JoaoVCMiranda/PSI3422/experiências/Exp3_PSI3422/modelo_1/print/hw201_bracket.scad

include <../parts/params.scad>
use <../parts/hw201_mount.scad>

hw201_bracket_3d(0, 0);
