JoaoVCMiranda/PSI3422/experiências/Exp3_PSI3422/modelo_3/print/hw201_bracket.scad

// Suporte do sensor HW-201 — imprimir 2x (um por roda, são idênticos,
// só a posição de montagem na chapa que muda).
include <../parts/params.scad>
use <../parts/hw201_mount.scad>

hw201_bracket_3d(motor_l_center);
