JoaoVCMiranda/PSI3422/experiências/Exp3_PSI3422/modelo_3/print/kl25z_standoff.scad

// Pé PCB shield->KL25Z — imprimir 2x.
include <../parts/params.scad>

cylinder(d = 5, h = kl25z_standoff_height, $fn = 16);
