JoaoVCMiranda/PSI3422/experiências/Exp3_PSI3422/modelo_3/print/pcb_standoff.scad

// Pé chapa->PCB shield — imprimir 4x.
include <../parts/params.scad>

cylinder(d = pcb_hole_inset * 1.6, h = pcb_standoff_height);
